polerix/HAL9000/Artwork/HAL9000_EYE.png

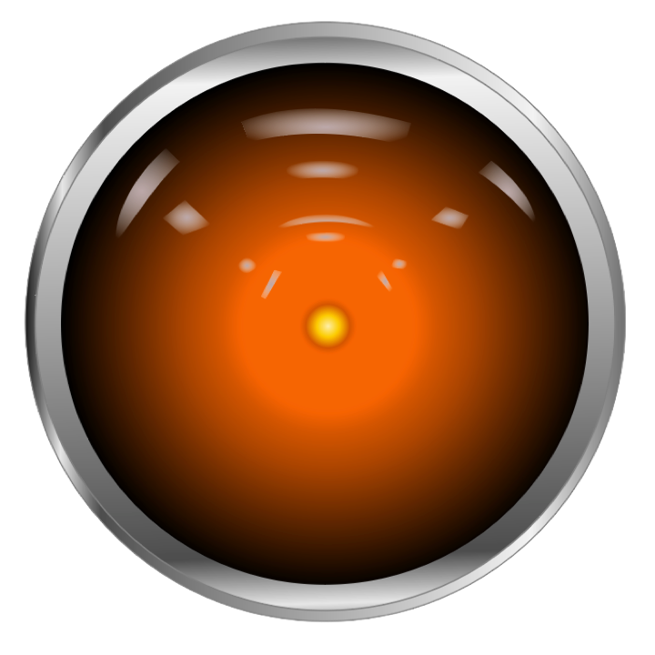
Artwork/HAL9000_EYE.png
