polerix/HAL9000/Artwork/Screenshot 2026-09-08 at 10.09.14 AM.png

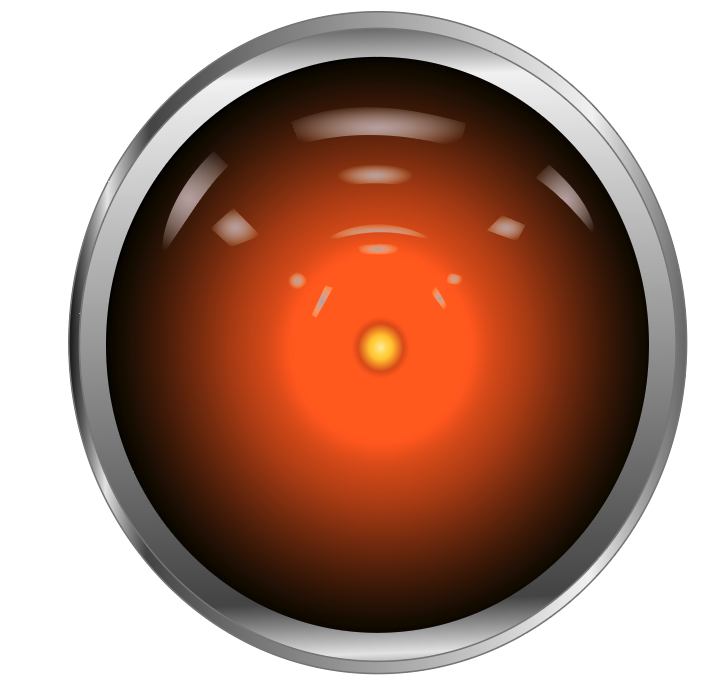
Artwork/Screenshot 2026-09-08 at 10.09.14 AM.png
