polerix/HAL9000/Images/HAL9000-punch-card-v1.jpg

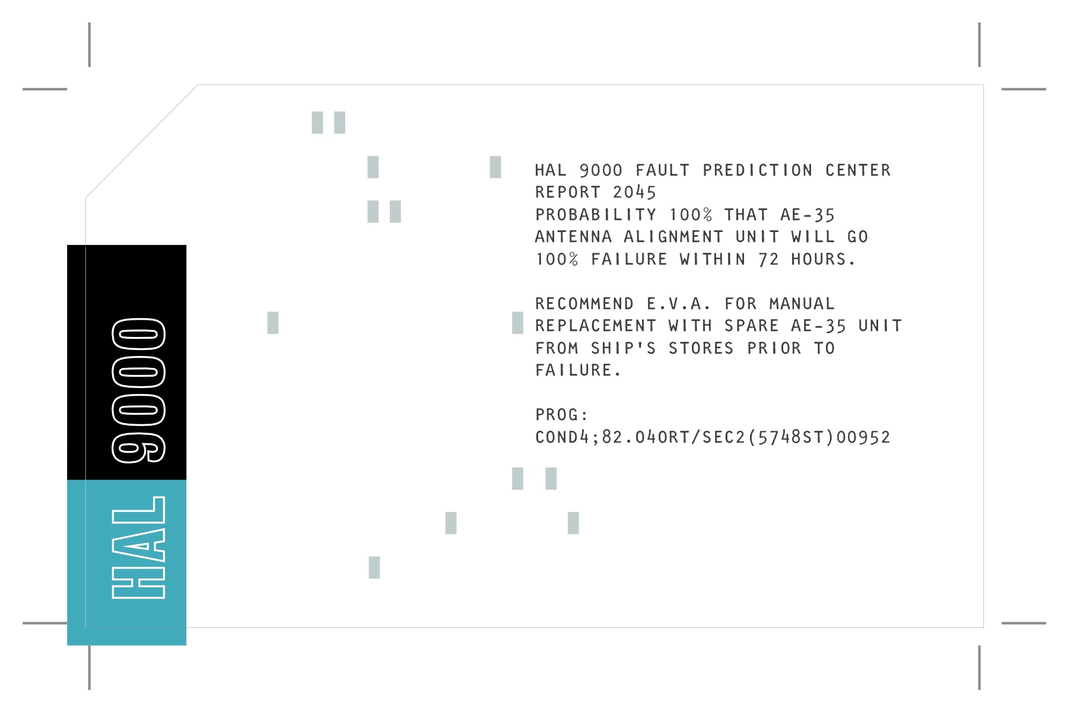
Images/HAL9000-punch-card-v1.jpg
