polerix/HAL9000/Images/HAL9000_Resources/hal2000screensaver-2.jpg

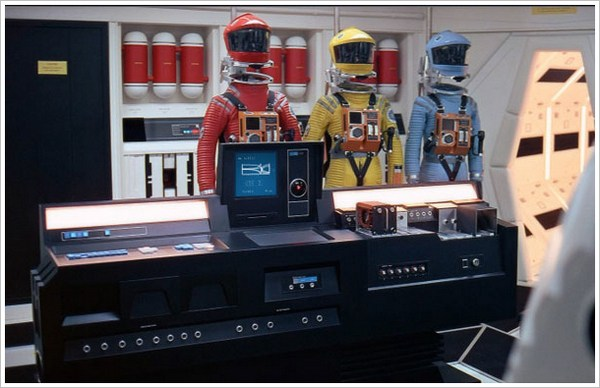
Images/HAL9000_Resources/hal2000screensaver-2.jpg
