polerix/HAL9000/Terminal_Parts/Silver Iris Ring.stl.stl

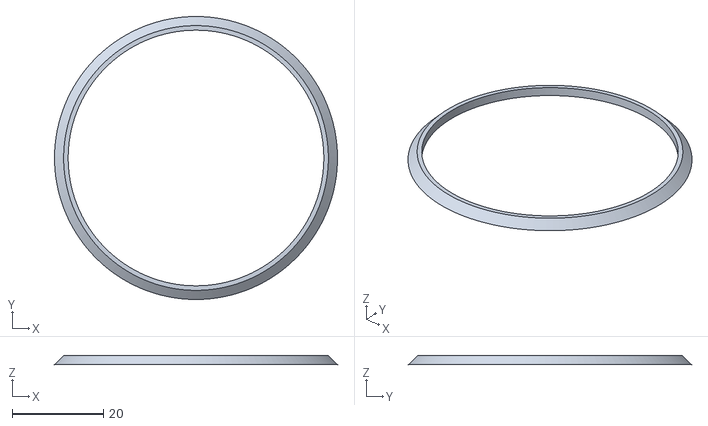
[picture p21: CAD file, 2026-08-20]
Terminal_Parts/Silver Iris Ring.stl.stl
62.0 x 62.0 x 2.00
