polerix/HAL9000/Terminal_Parts/Black Iris Border.stl.stl

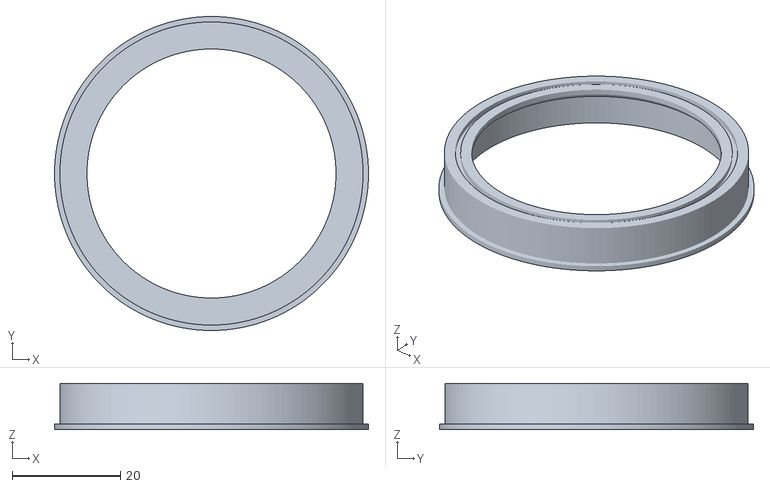
[picture p22: CAD file, 2026-08-20]
Terminal_Parts/Black Iris Border.stl.stl
58.0 x 58.0 x 8.50
