polerix/HAL9000/Terminal_Parts/Silver Iris Panel.stl.stl

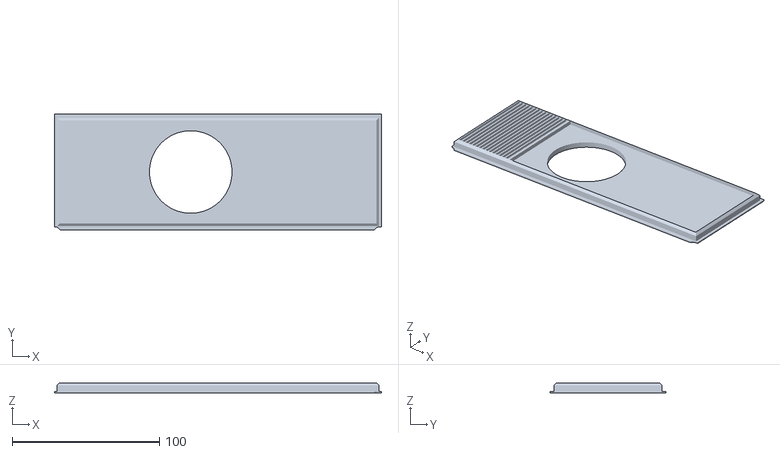
[picture p23: CAD file, 2026-08-20]
Terminal_Parts/Silver Iris Panel.stl.stl
222.0 x 79.0 x 7.00
