polerix/HAL9000/Images/HAL9000_Terminal_Build_Card-04.webp

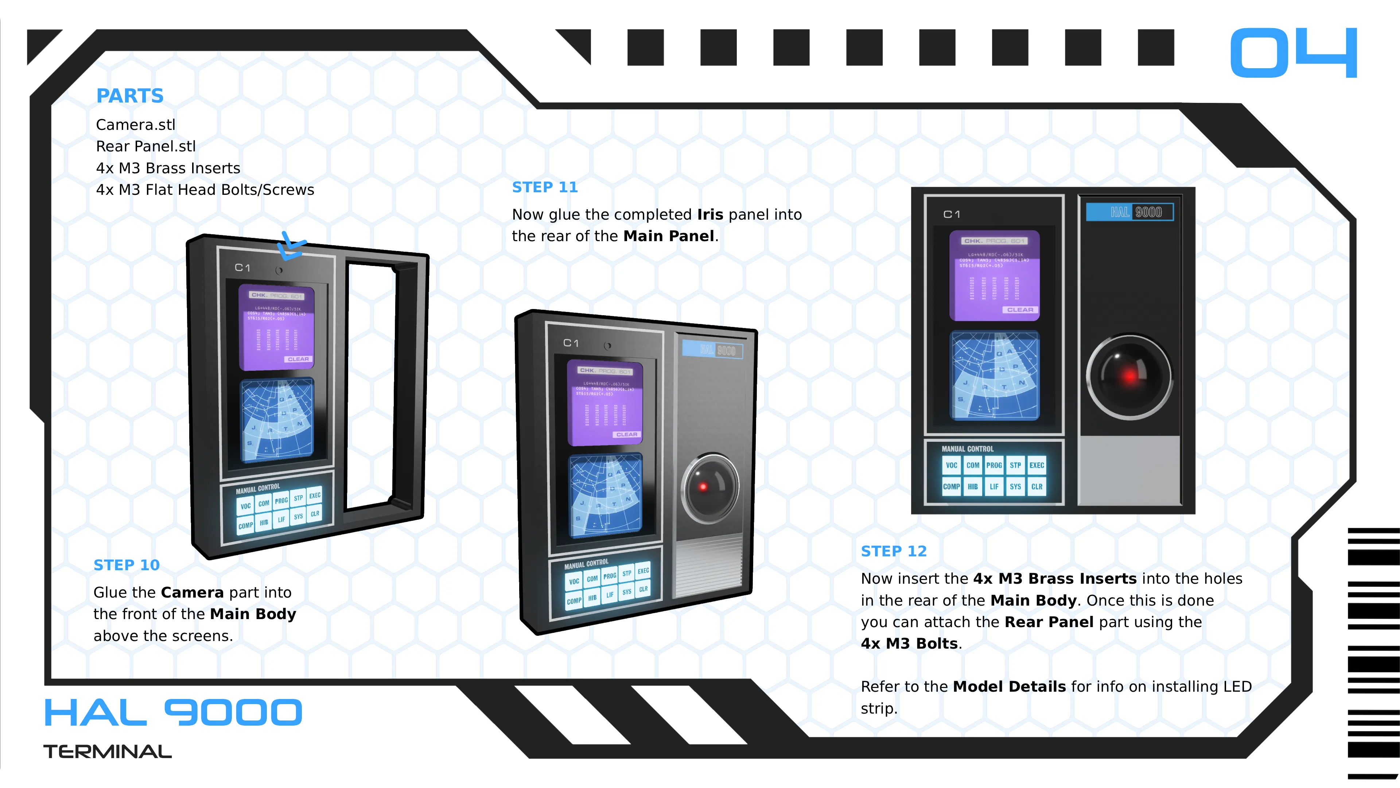
Images/HAL9000_Terminal_Build_Card-04.webp
